NoahMSchool/RobotArmEPQ/Images/Screenshot 2025-09-12 at 22.15.42.png

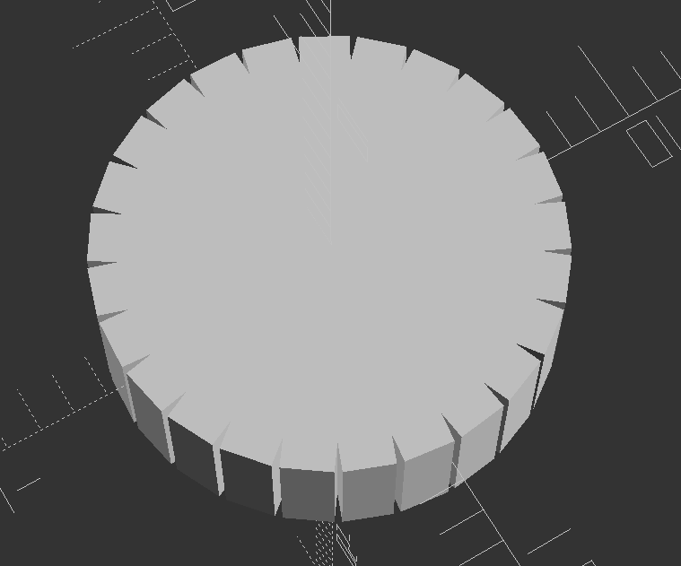
Images/Screenshot 2025-09-12 at 22.15.42.png
