NoahMSchool/RobotArmEPQ/Images/Screenshot 2025-09-20 at 10.08.07.png

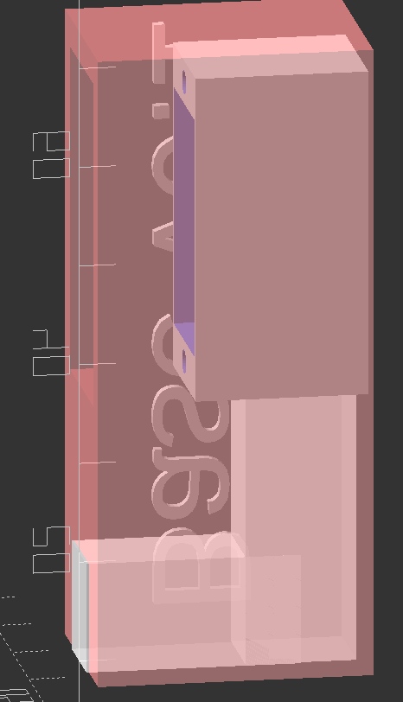
Images/Screenshot 2025-09-20 at 10.08.07.png
