NoahMSchool/RobotArmEPQ/EPQCAD/stlfiles/servos/MG996R_servo_offset_box.stl

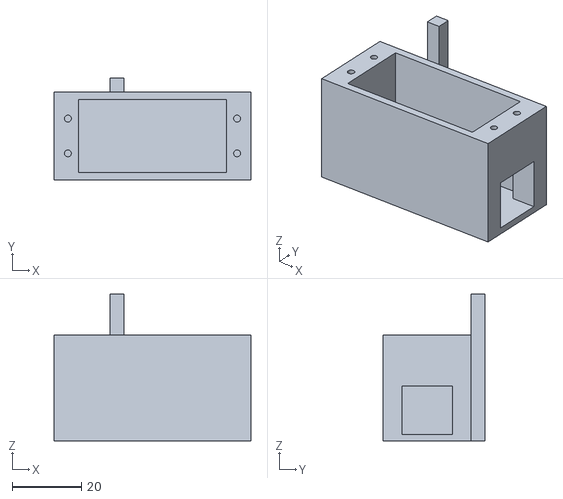
[picture p23: CAD file, 2025-10-07]
EPQCAD/stlfiles/servos/MG996R_servo_offset_box.stl
56.7 x 29.4 x 42.3
