NoahMSchool/RobotArmEPQ/EPQCAD/stlfiles/ReadyActivityMagnet.stl

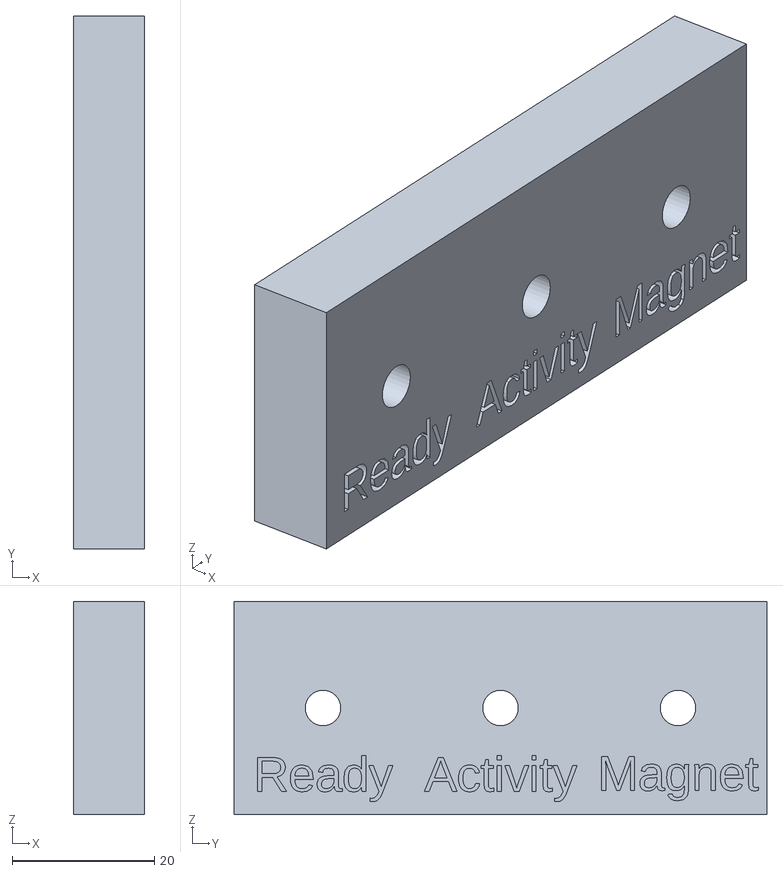
[picture p24: CAD file, 2025-10-24]
EPQCAD/stlfiles/ReadyActivityMagnet.stl
10.0 x 75.0 x 30.0
