NoahMSchool/RobotArmEPQ/EPQCAD/stlfiles/servos/MG996R_shafttestv2.stl

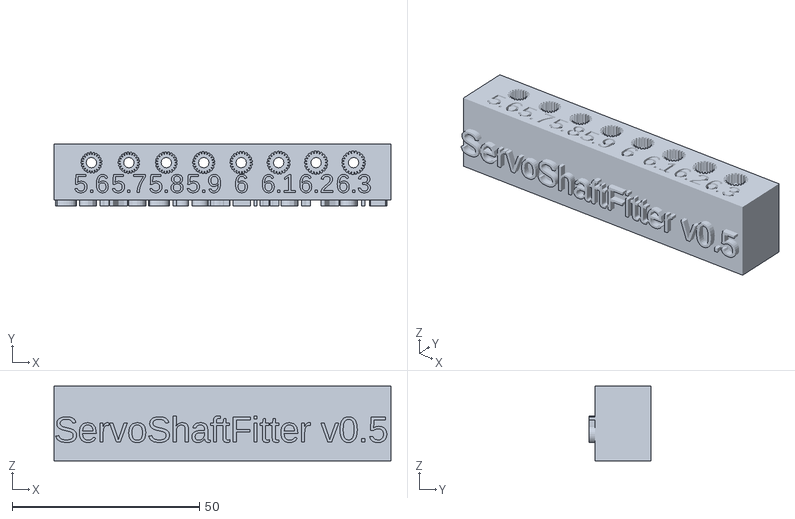
[picture p25: CAD file, 2025-10-07]
EPQCAD/stlfiles/servos/MG996R_shafttestv2.stl
90.0 x 16.6 x 20.0
