NoahMSchool/RobotArmEPQ/EPQCAD/stlfiles/base_wall1.stl

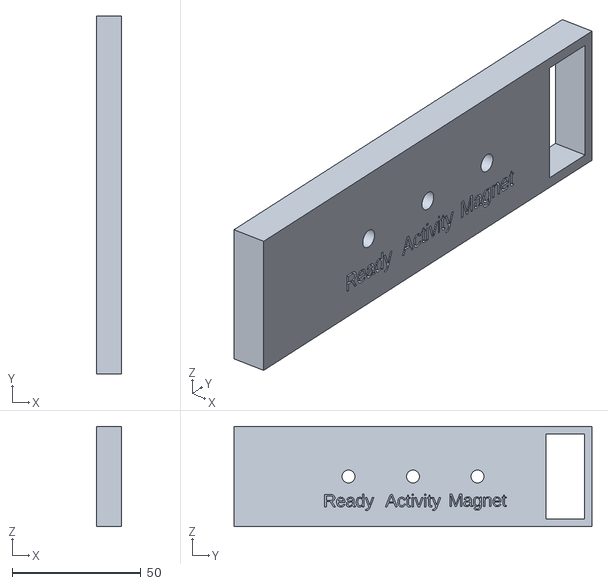
[picture p26: CAD file, 2025-10-24]
EPQCAD/stlfiles/base_wall1.stl
9.80 x 138.8 x 38.8
