NoahMSchool/RobotArmEPQ/EPQCAD/stlfiles/servos/MG92B_servo_v1.stl

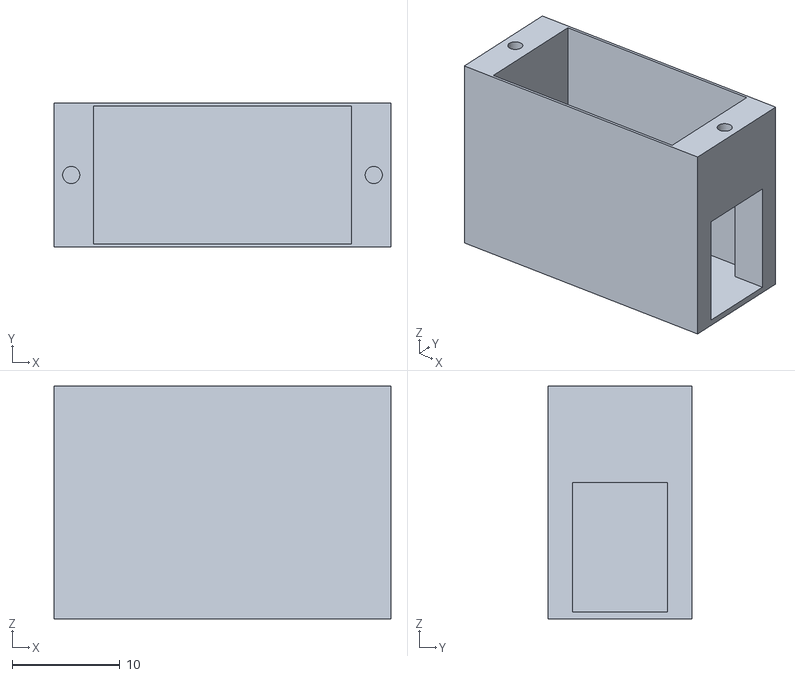
[picture p27: CAD file, 2025-10-07]
EPQCAD/stlfiles/servos/MG92B_servo_v1.stl
31.3 x 13.4 x 21.6
