NoahMSchool/RobotArmEPQ/EPQCAD/stlfiles/magbeam5.stl

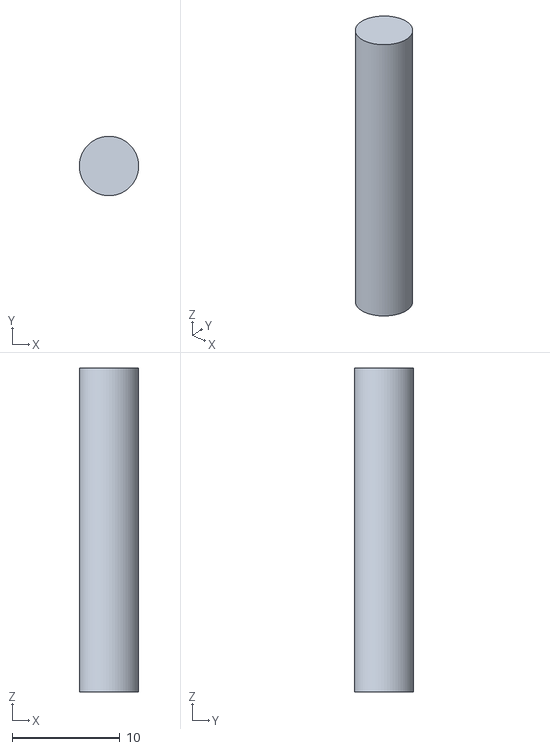
[picture p28: CAD file, 2025-10-24]
EPQCAD/stlfiles/magbeam5.stl
5.50 x 5.50 x 30.0
