NoahMSchool/RobotArmEPQ/EPQCAD/stlfiles/basewall4.stl

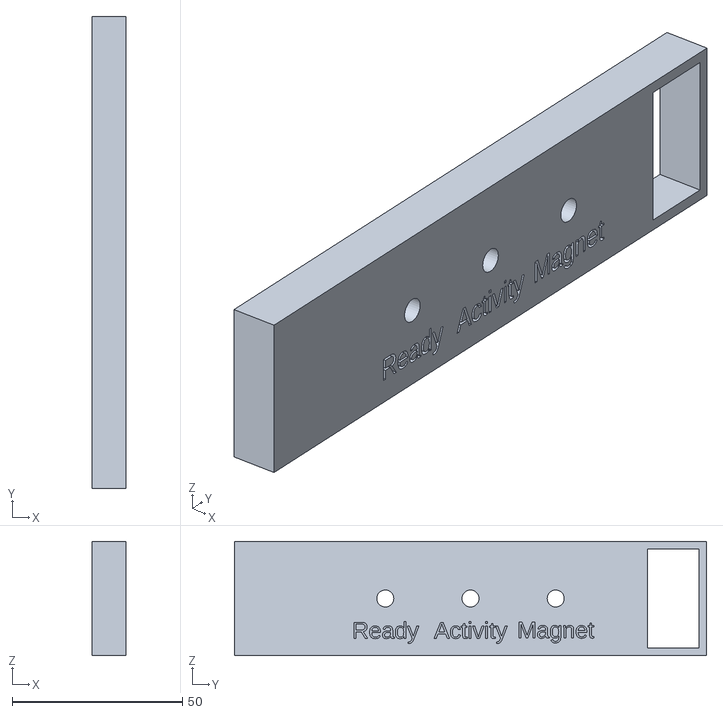
[picture p29: CAD file, 2025-10-24]
EPQCAD/stlfiles/basewall4.stl
10.0 x 138.5 x 33.5
