NoahMSchool/RobotArmEPQ/EPQCAD/stlfiles/basewall3.stl

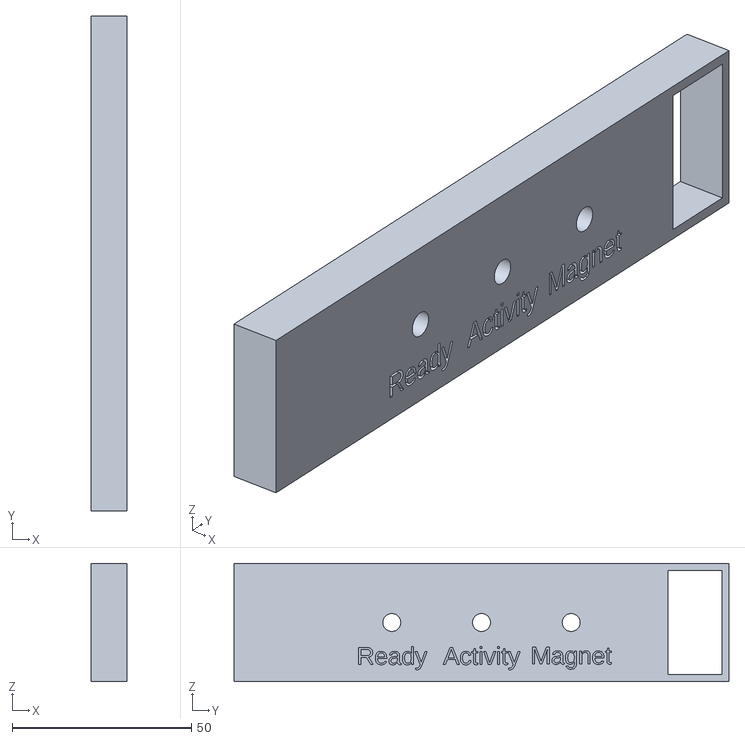
[picture p30: CAD file, 2025-10-24]
EPQCAD/stlfiles/basewall3.stl
10.0 x 138.0 x 33.0
