NoahMSchool/RobotArmEPQ/EPQCAD/stlfiles/servos/SG90servo4.stl

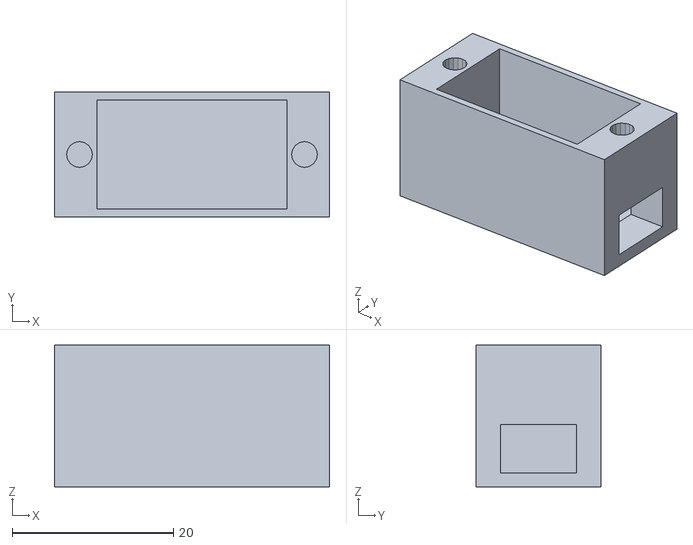
[picture p31: CAD file, 2025-08-15]
EPQCAD/stlfiles/servos/SG90servo4.stl
34.1 x 15.5 x 17.6
