NoahMSchool/RobotArmEPQ/EPQCAD/stlfiles/servos/SG90servo6.stl

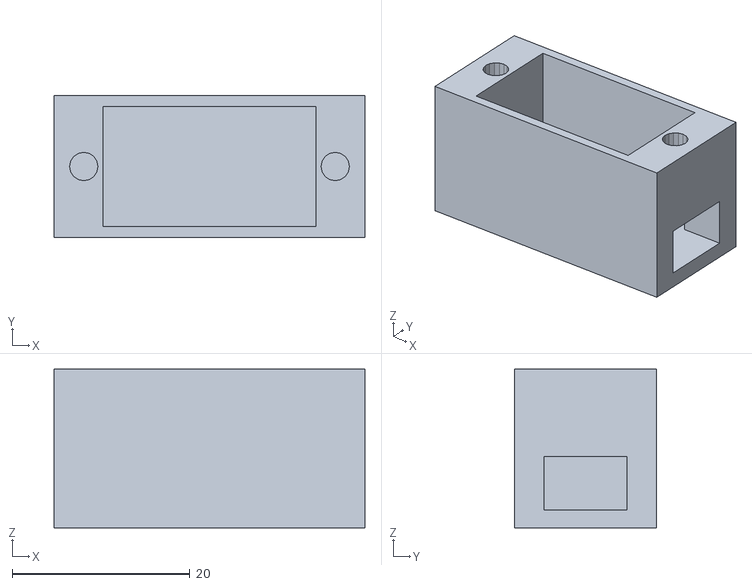
[picture p32: CAD file, 2025-08-15]
EPQCAD/stlfiles/servos/SG90servo6.stl
35.0 x 16.0 x 17.8
