NoahMSchool/RobotArmEPQ/EPQCAD/stlfiles/electromag6.stl

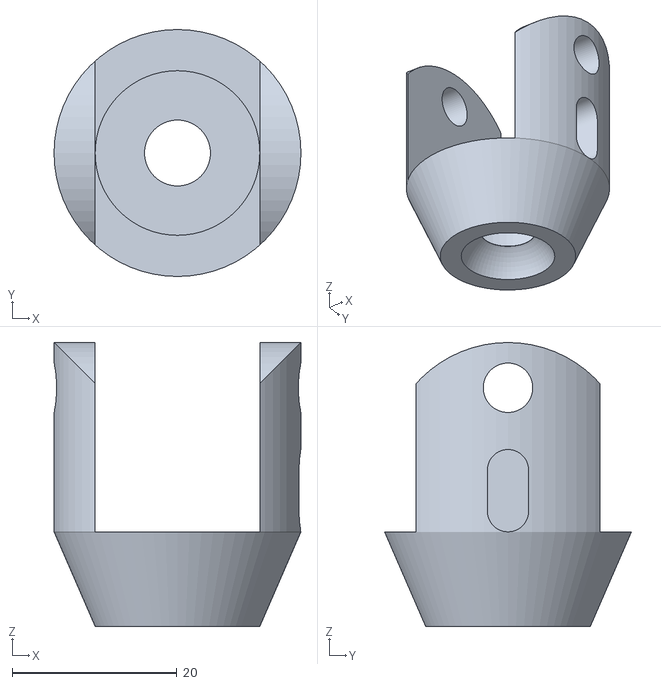
[picture p33: CAD file, 2025-10-24]
EPQCAD/stlfiles/electromag6.stl
30.0 x 30.0 x 34.5
