NoahMSchool/RobotArmEPQ/EPQCAD/stlfiles/servos/sg90servo7.stl

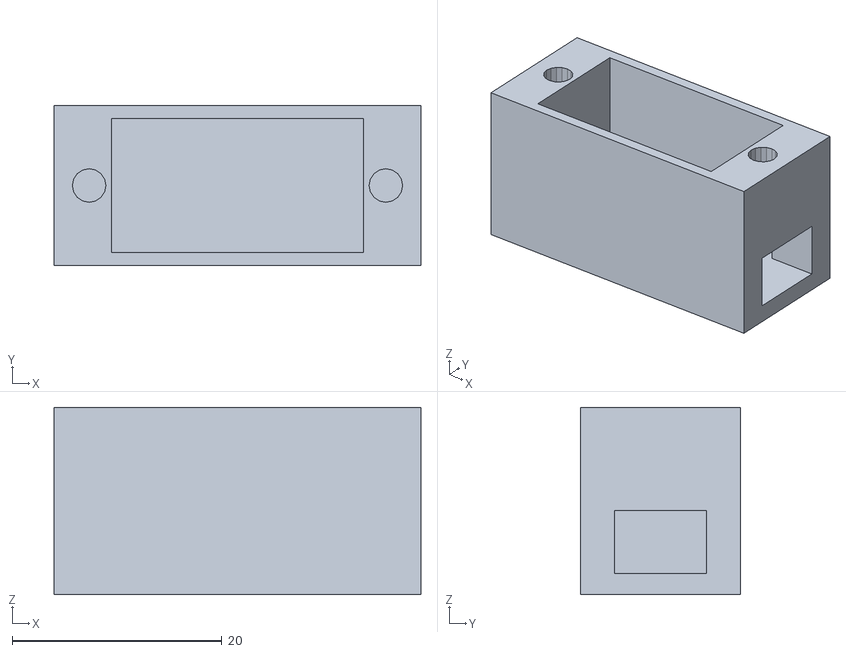
[picture p34: CAD file, 2025-08-15]
EPQCAD/stlfiles/servos/sg90servo7.stl
35.0 x 15.2 x 17.8
