NoahMSchool/RobotArmEPQ/EPQCAD/stlfiles/electromag5.stl

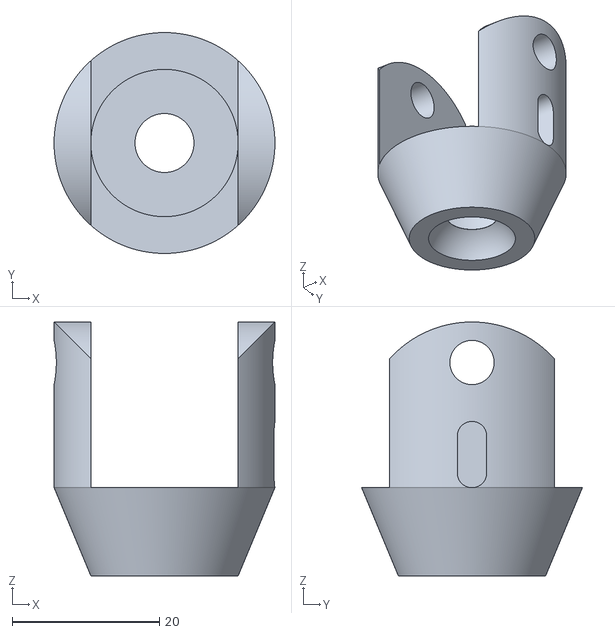
[picture p35: CAD file, 2025-10-24]
EPQCAD/stlfiles/electromag5.stl
30.0 x 30.0 x 34.5
