NoahMSchool/RobotArmEPQ/EPQCAD/stlfiles/servos/SG90MS1818servo2.stl

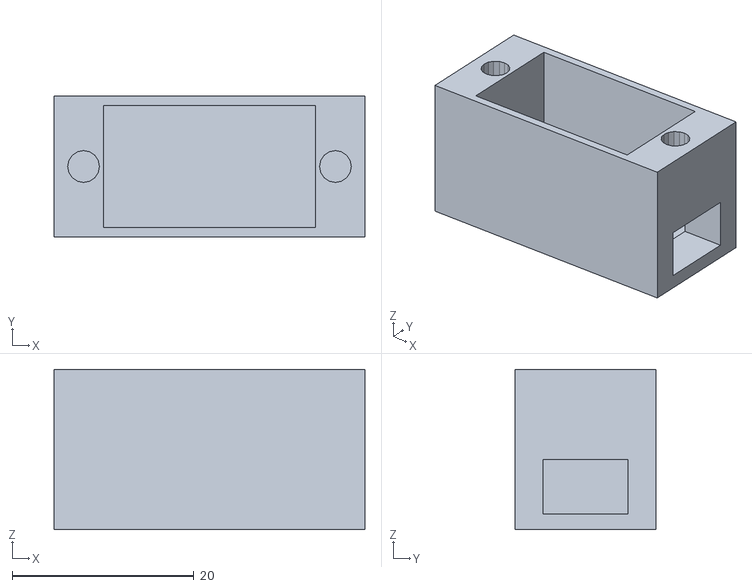
[picture p36: CAD file, 2025-08-15]
EPQCAD/stlfiles/servos/SG90MS1818servo2.stl
34.2 x 15.5 x 17.6
