NoahMSchool/RobotArmEPQ/EPQCAD/stlfiles/servos/sg90servocontainer2.stl

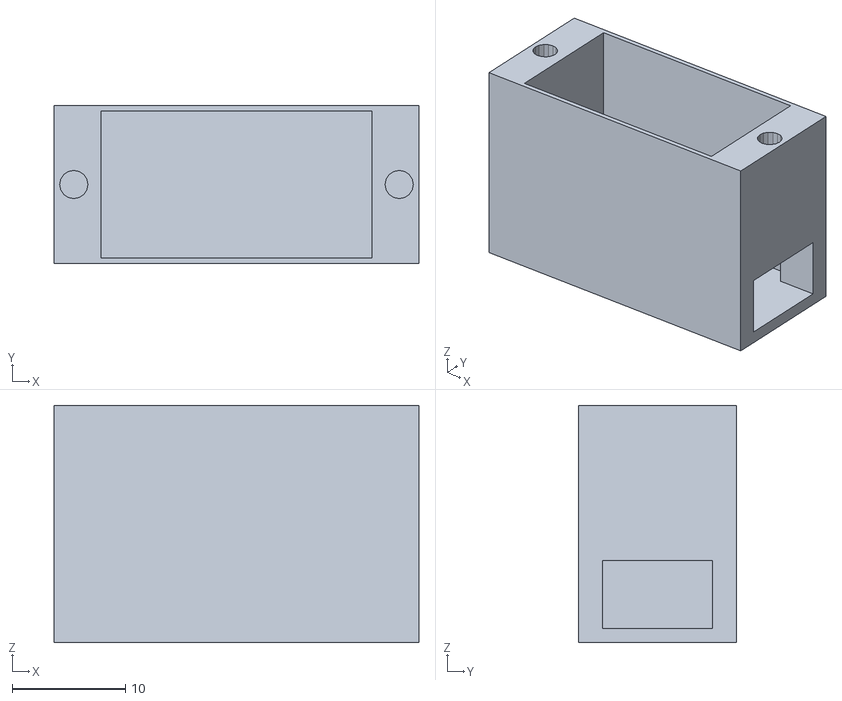
[picture p37: CAD file, 2025-08-15]
EPQCAD/stlfiles/servos/sg90servocontainer2.stl
32.3 x 14.0 x 21.0
