NoahMSchool/RobotArmEPQ/EPQCAD/stlfiles/servos/servoSG90_top.stl

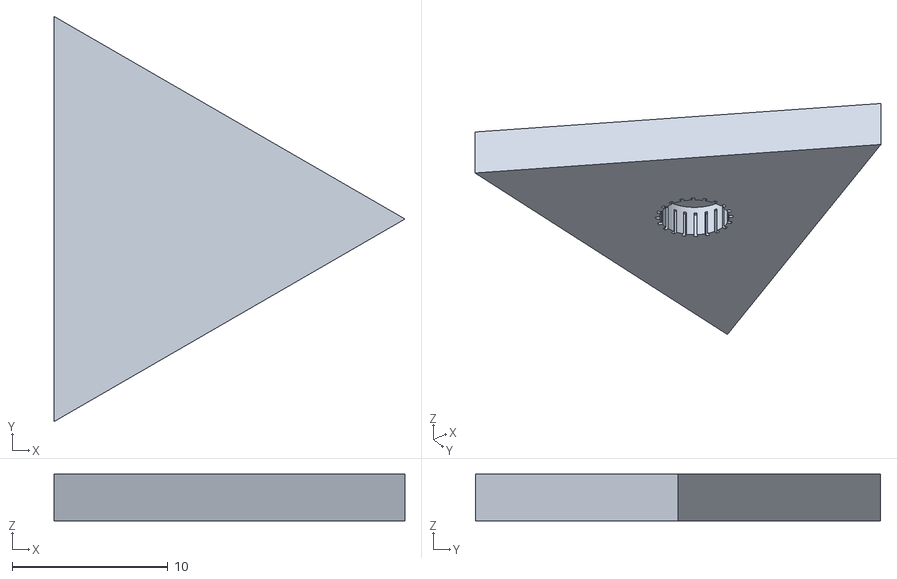
[picture p38: CAD file, 2025-08-15]
EPQCAD/stlfiles/servos/servoSG90_top.stl
22.5 x 26.0 x 3.00
