NoahMSchool/RobotArmEPQ/EPQCAD/stlfiles/effector_segmentV405.stl

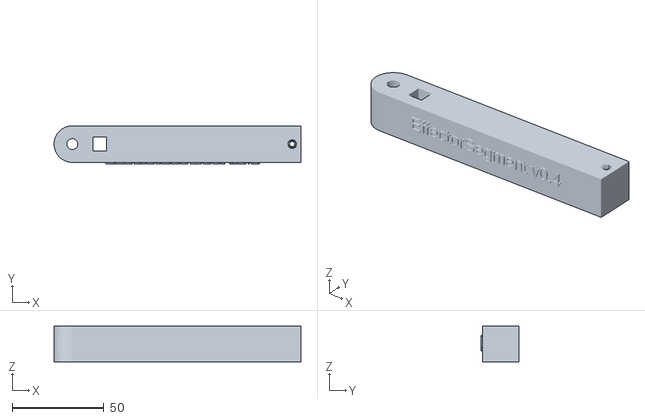
[picture p39: CAD file, 2025-10-13]
EPQCAD/stlfiles/effector_segmentV405.stl
134.8 x 21.0 x 19.5
