NoahMSchool/RobotArmEPQ/EPQCAD/stlfiles/servos/SG90servo5.stl

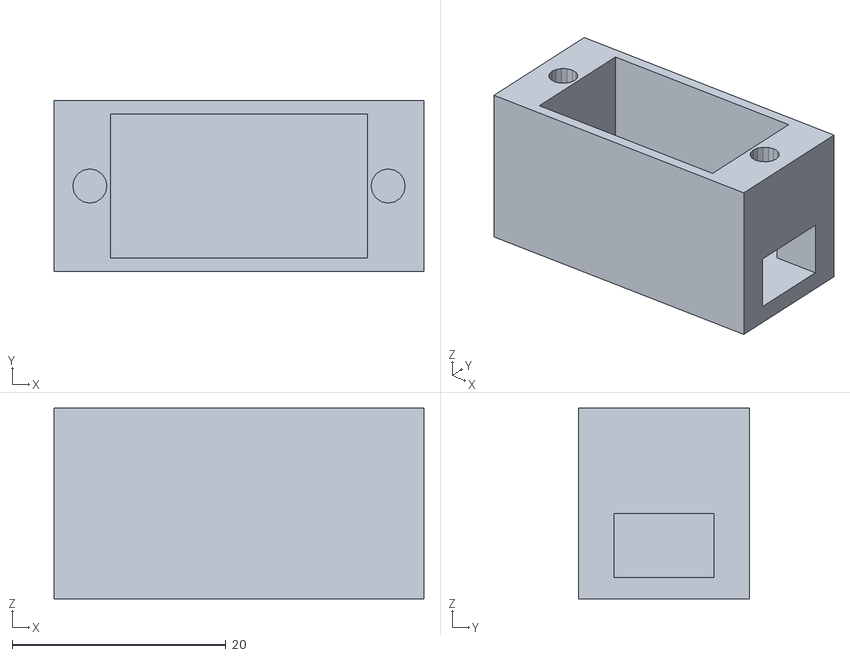
[picture p40: CAD file, 2025-08-15]
EPQCAD/stlfiles/servos/SG90servo5.stl
34.6 x 16.0 x 17.8
