NoahMSchool/RobotArmEPQ/EPQCAD/stlfiles/middle_seg_v4.stl

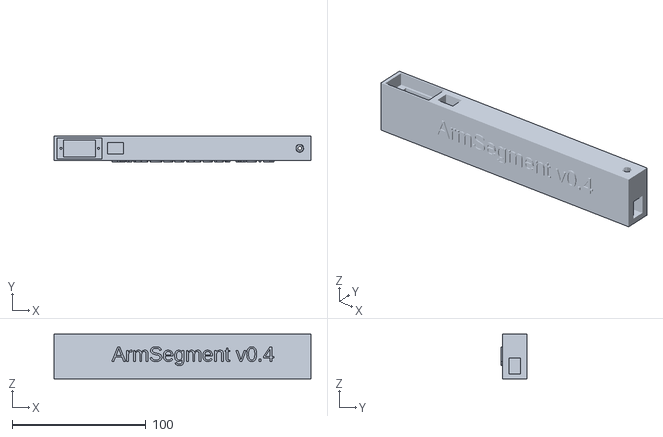
[picture p41: CAD file, 2025-10-13]
EPQCAD/stlfiles/middle_seg_v4.stl
192.5 x 19.2 x 33.3
