NoahMSchool/RobotArmEPQ/EPQCAD/stlfiles/servos/robot_arm.stl

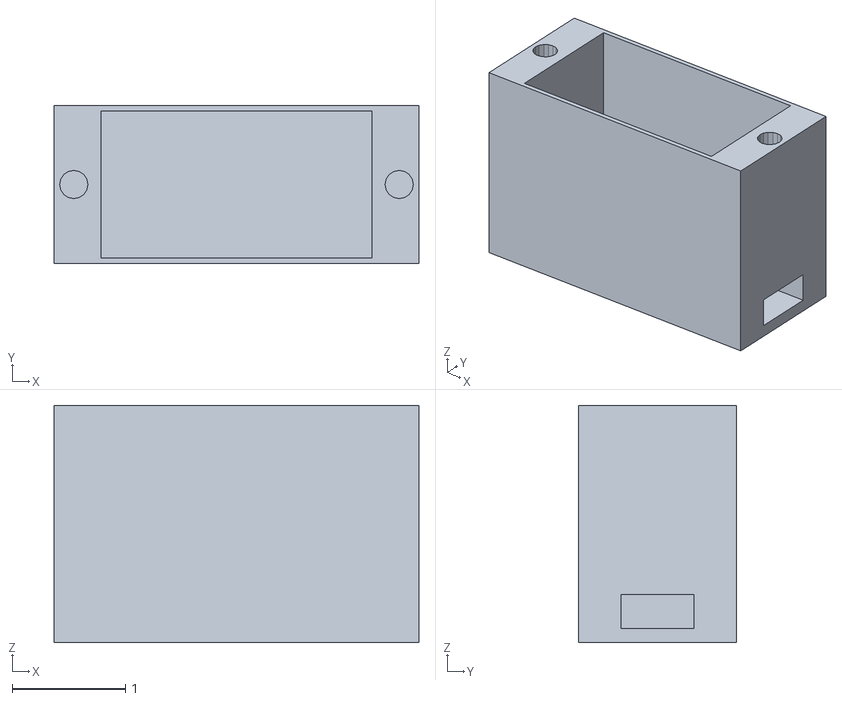
[picture p42: CAD file, 2025-08-15]
EPQCAD/stlfiles/servos/robot_arm.stl
3.23 x 1.40 x 2.10
