NoahMSchool/RobotArmEPQ/EPQCAD/stlfiles/MG996R_shaftfitter_1.stl

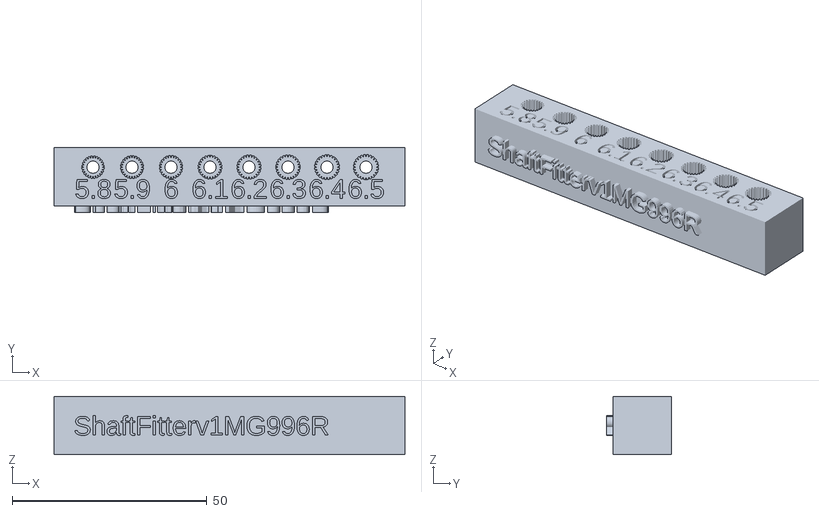
[picture p43: CAD file, 2025-10-13]
EPQCAD/stlfiles/MG996R_shaftfitter_1.stl
90.0 x 16.6 x 15.0
