NoahMSchool/RobotArmEPQ/EPQCAD/stlfiles/shaft_testv6.stl

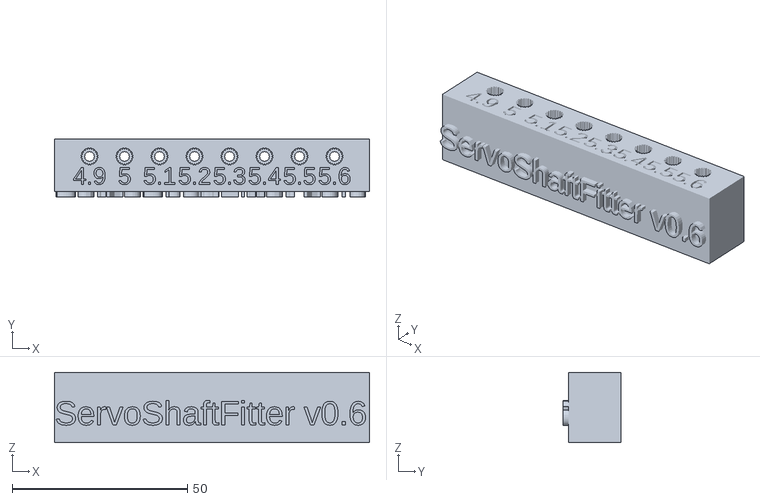
[picture p44: CAD file, 2025-10-13]
EPQCAD/stlfiles/shaft_testv6.stl
90.0 x 16.6 x 20.0
