NoahMSchool/RobotArmEPQ/EPQCAD/stlfiles/magnet_beam_1.stl

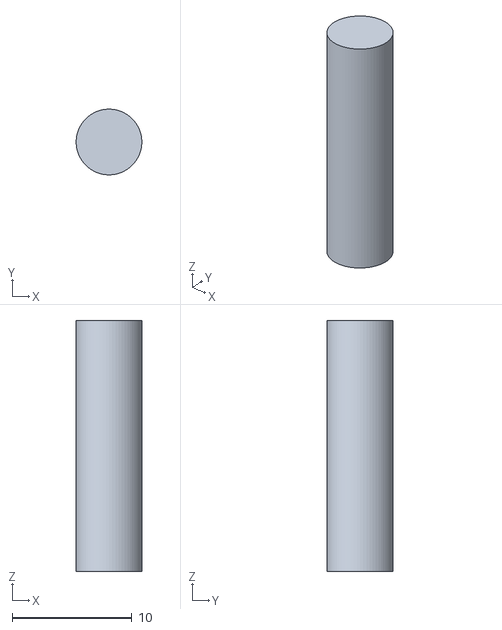
[picture p45: CAD file, 2025-10-13]
EPQCAD/stlfiles/magnet_beam_1.stl
5.50 x 5.50 x 21.0
