NoahMSchool/RobotArmEPQ/EPQCAD/stlfiles/base_v03.stl

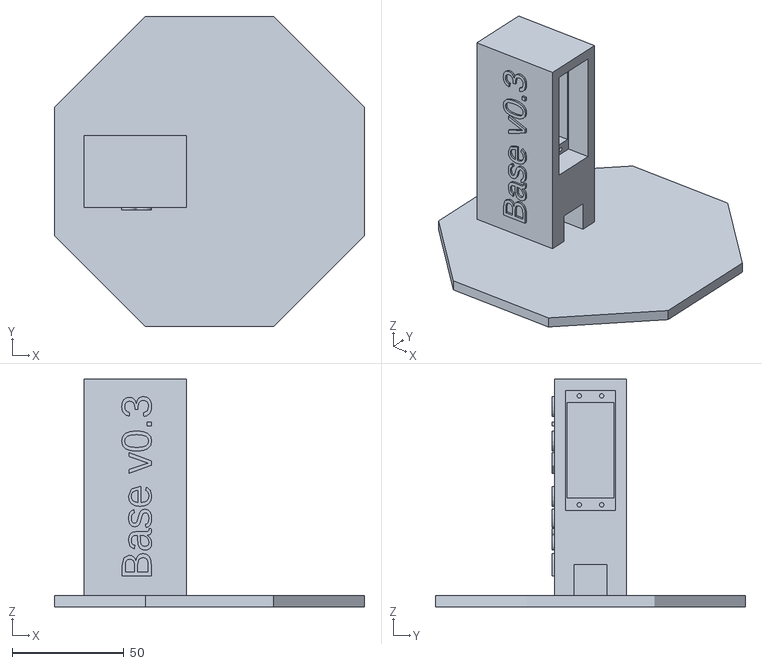
[picture p46: CAD file, 2025-09-28]
EPQCAD/stlfiles/base_v03.stl
138.6 x 138.6 x 101.8
