NoahMSchool/RobotArmEPQ/EPQCAD/stlfiles/EffectorSegment v01.stl

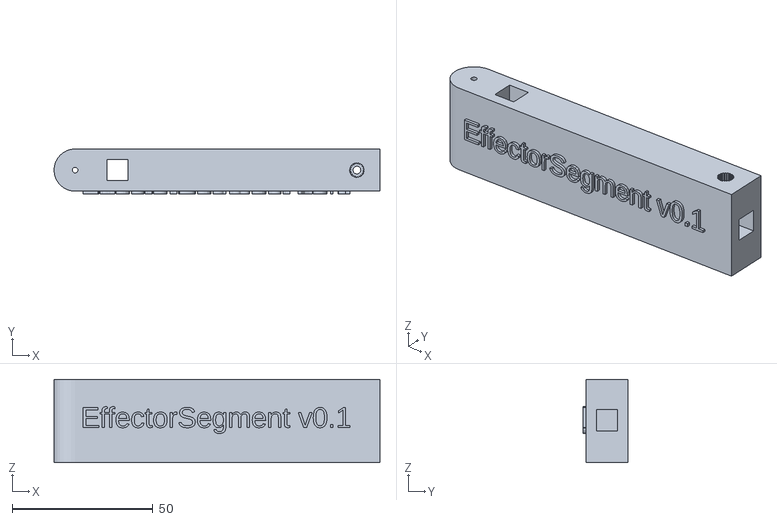
[picture p47: CAD file, 2025-09-28]
EPQCAD/stlfiles/EffectorSegment v01.stl
115.7 x 16.0 x 29.5
