NoahMSchool/RobotArmEPQ/EPQCAD/stlfiles/mgBase_v02.stl

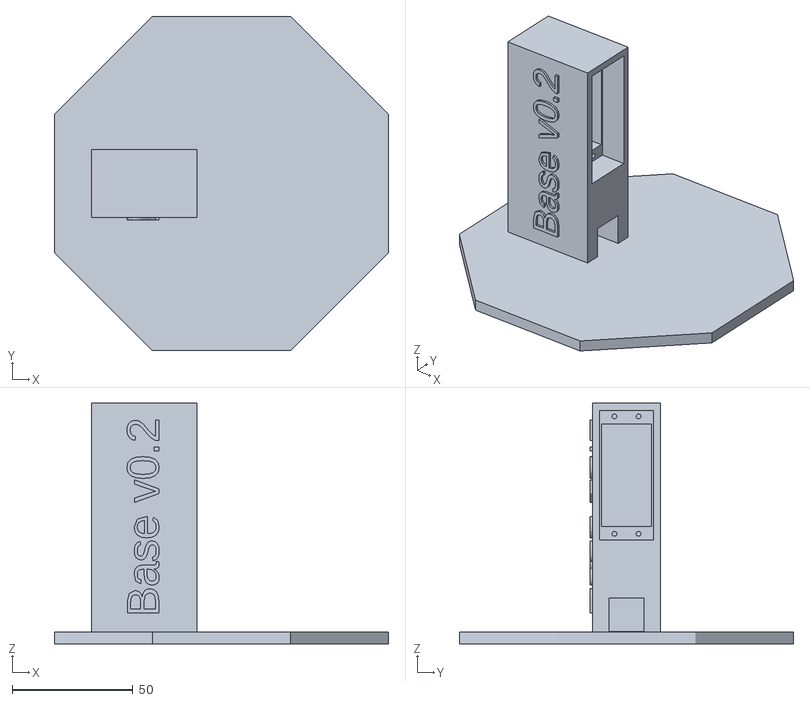
[picture p48: CAD file, 2025-09-28]
EPQCAD/stlfiles/mgBase_v02.stl
138.6 x 138.6 x 99.8
