NoahMSchool/RobotArmEPQ/EPQCAD/stlfiles/shaft_test5.stl

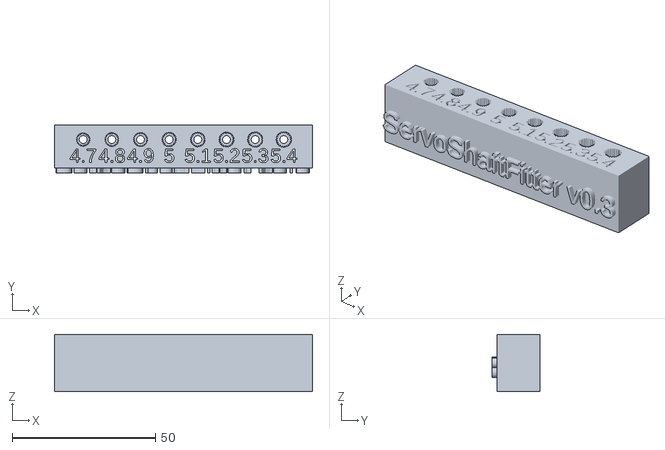
[picture p49: CAD file, 2025-09-24]
EPQCAD/stlfiles/shaft_test5.stl
90.0 x 16.6 x 20.0
