NoahMSchool/RobotArmEPQ/EPQCAD/stlfiles/SG90ShaftTest4.stl

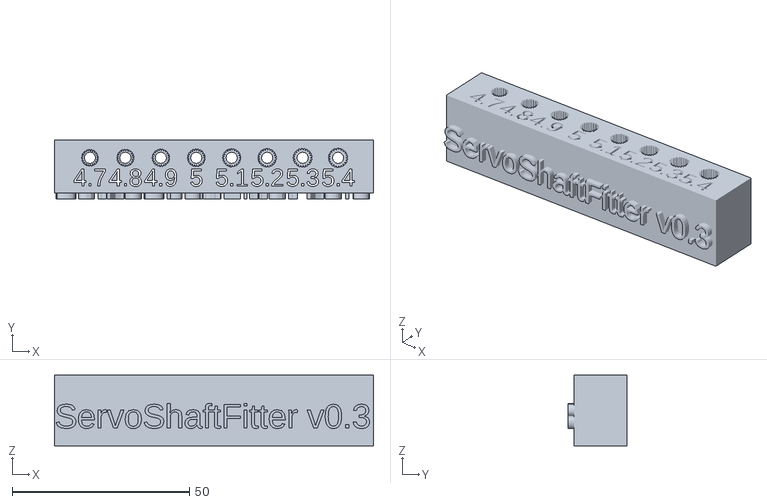
[picture p50: CAD file, 2025-09-24]
EPQCAD/stlfiles/SG90ShaftTest4.stl
90.0 x 16.6 x 20.0
