NoahMSchool/RobotArmEPQ/EPQCAD/stlfiles/middlearmsegmentv04.stl

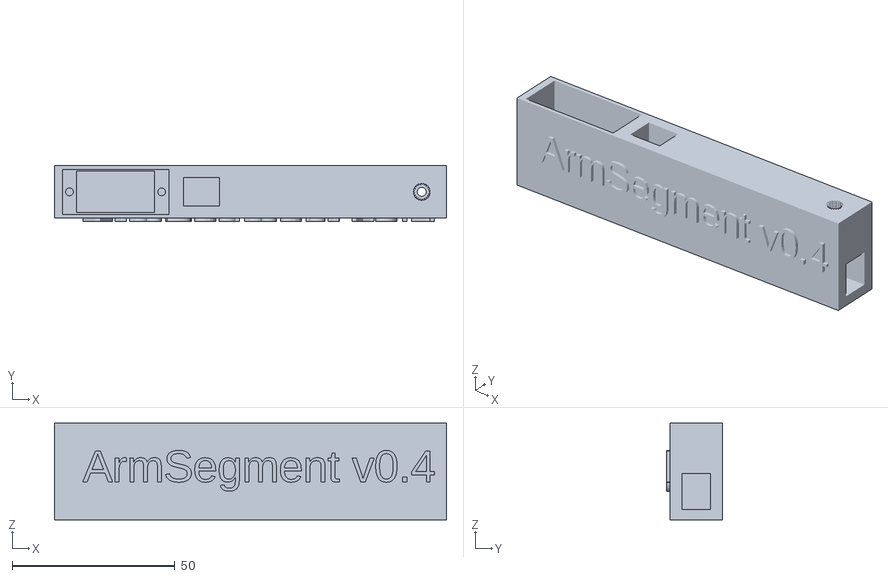
[picture p51: CAD file, 2025-09-24]
EPQCAD/stlfiles/middlearmsegmentv04.stl
120.3 x 17.1 x 29.6
