NoahMSchool/RobotArmEPQ/EPQCAD/stlfiles/basev01.stl

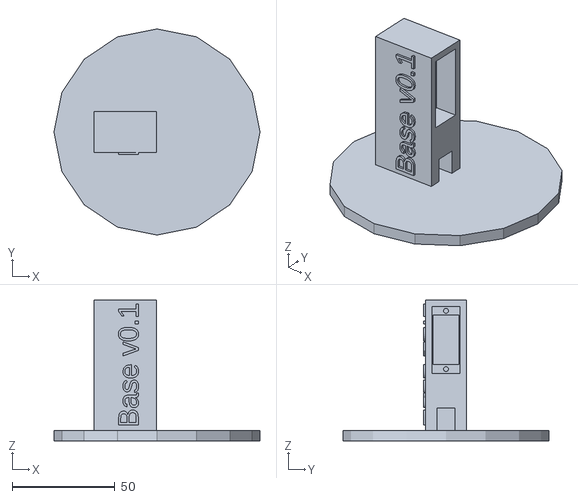
[picture p52: CAD file, 2025-09-24]
EPQCAD/stlfiles/basev01.stl
100.0 x 100.0 x 68.3
