NoahMSchool/RobotArmEPQ/EPQCAD/stlfiles/SG90shafttest2.stl

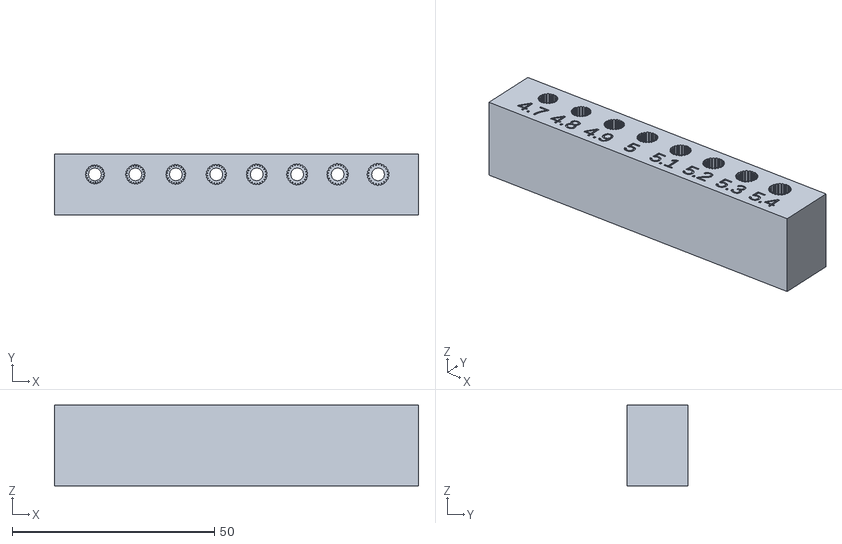
[picture p53: CAD file, 2025-09-18]
EPQCAD/stlfiles/SG90shafttest2.stl
90.0 x 15.0 x 20.0
