NoahMSchool/RobotArmEPQ/EPQCAD/stlfiles/middlearmsegment3.stl

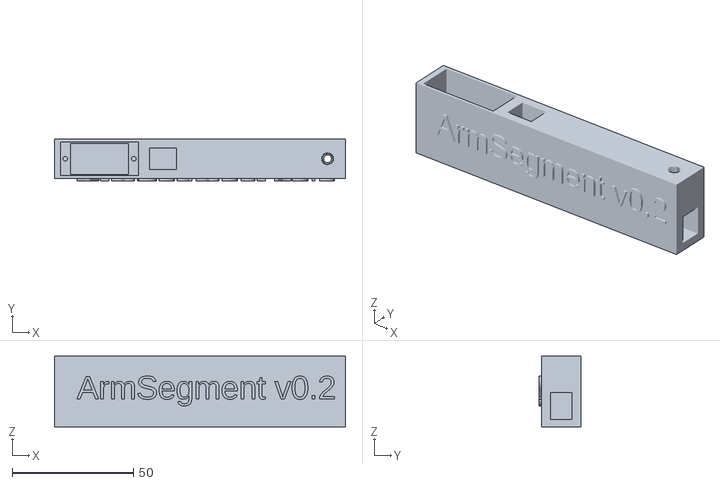
[picture p54: CAD file, 2025-09-13]
EPQCAD/stlfiles/middlearmsegment3.stl
120.0 x 17.1 x 29.2
