NoahMSchool/RobotArmEPQ/EPQCAD/stlfiles/middlearmsegment2.stl

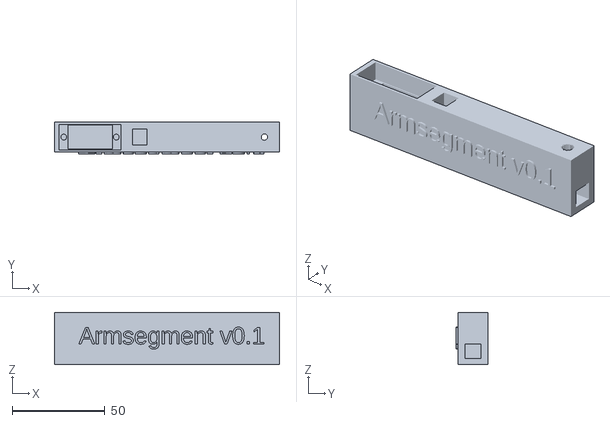
[picture p55: CAD file, 2025-09-13]
EPQCAD/stlfiles/middlearmsegment2.stl
121.2 x 17.1 x 28.0
