NoahMSchool/RobotArmEPQ/EPQCAD/stlfiles/middleseg1.stl

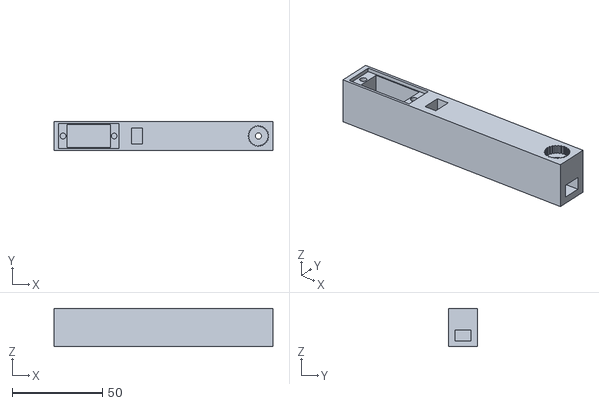
[picture p56: CAD file, 2025-09-13]
EPQCAD/stlfiles/middleseg1.stl
121.2 x 16.1 x 21.2
