NoahMSchool/RobotArmEPQ/EPQCAD/stlfiles/Mg996Rservo2.stl

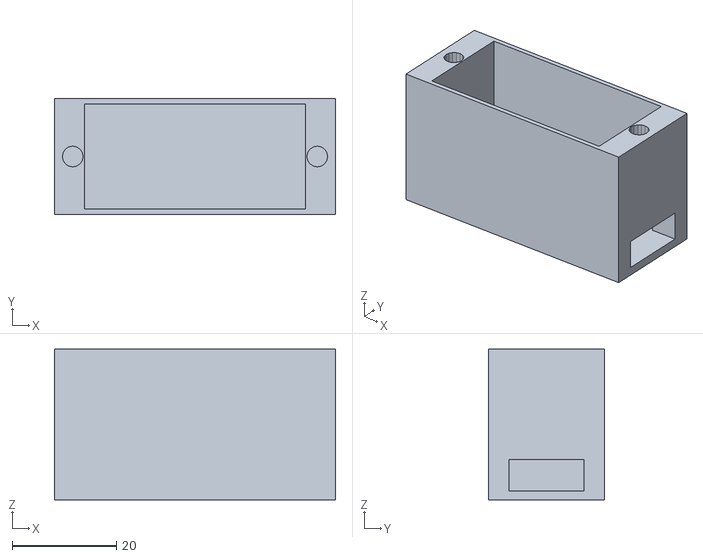
[picture p57: CAD file, 2025-08-23]
EPQCAD/stlfiles/Mg996Rservo2.stl
54.0 x 22.2 x 29.0
