NoahMSchool/RobotArmEPQ/EPQCAD/stlfiles/MG996Rservo3.stl

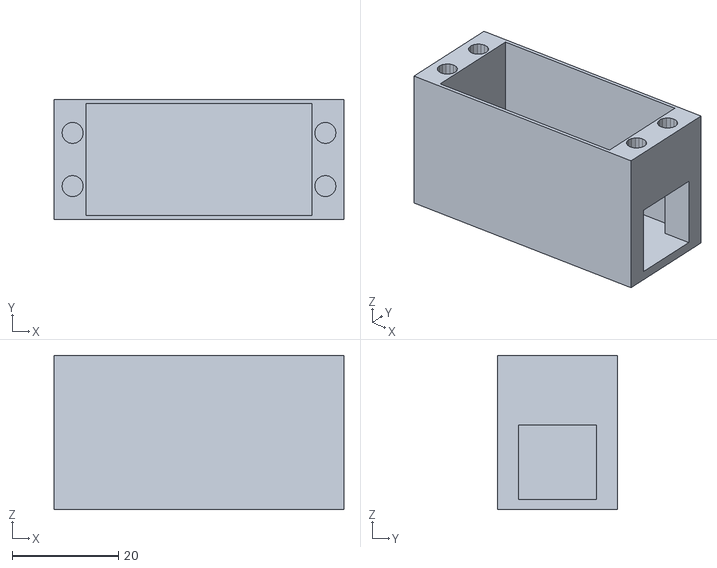
[picture p58: CAD file, 2025-08-23]
EPQCAD/stlfiles/MG996Rservo3.stl
54.5 x 22.5 x 29.0
