NoahMSchool/RobotArmEPQ/EPQCAD/stlfiles/electromagnet1.stl

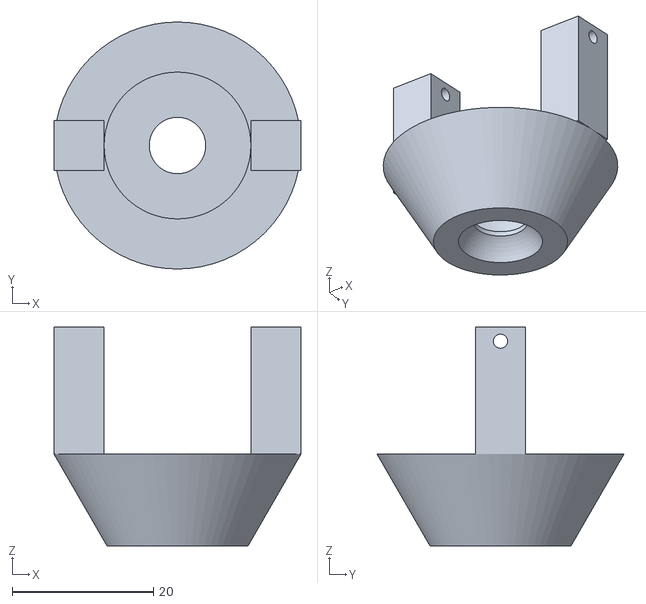
[picture p59: CAD file, 2025-08-22]
EPQCAD/stlfiles/electromagnet1.stl
35.0 x 35.0 x 31.0
