NoahMSchool/RobotArmEPQ/EPQCAD/stlfiles/MG996Rservo1.stl

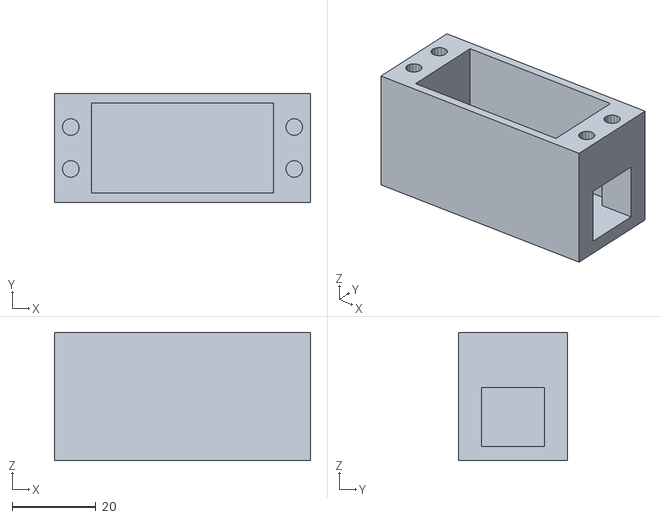
[picture p60: CAD file, 2025-08-22]
EPQCAD/stlfiles/MG996Rservo1.stl
61.0 x 26.0 x 30.5
